gkanwar/unchat-keeb/images/unchat_2023/3d.png

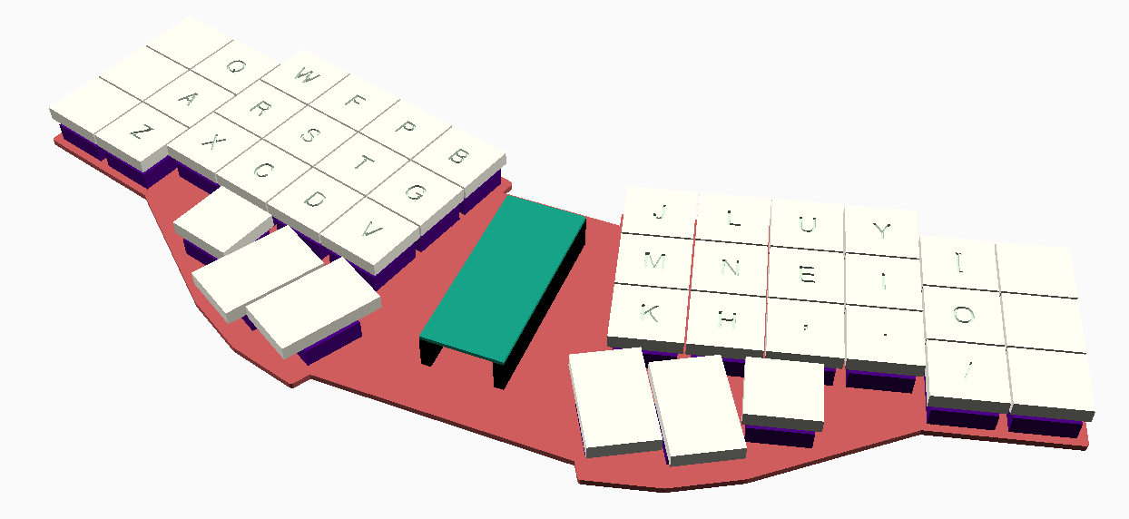
images/unchat_2023/3d.png
