gkanwar/unchat-keeb/images/unchat_2023/photo_top_no_keycaps.jpg

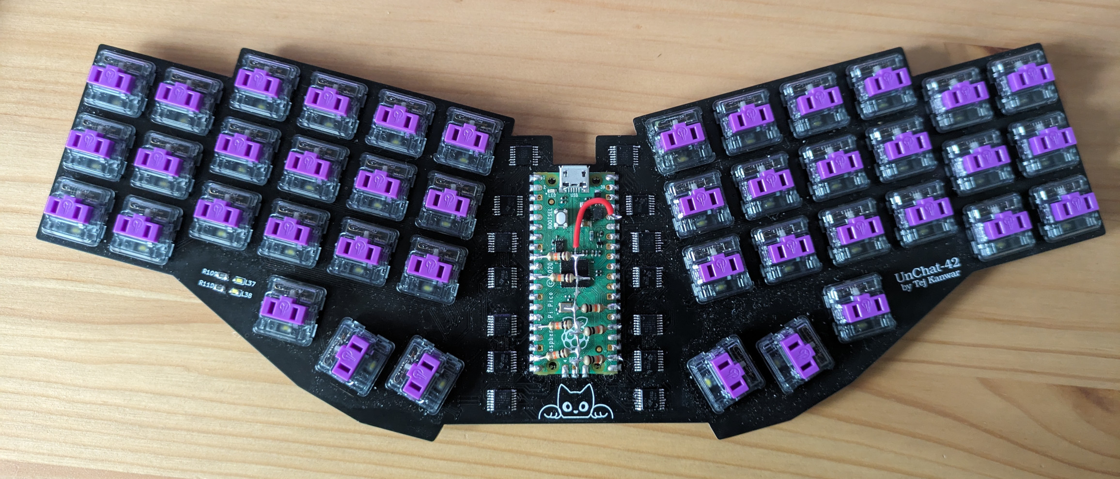
images/unchat_2023/photo_top_no_keycaps.jpg
