gkanwar/unchat-keeb/images/unchat_2024/photo_both_no_keycaps.jpg

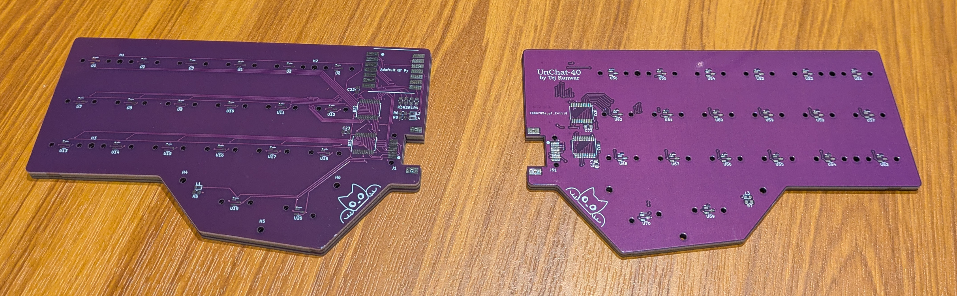
images/unchat_2024/photo_both_no_keycaps.jpg
