gkanwar/unchat-keeb/images/unchat_2024/photo_rhs_no_keycaps.jpg

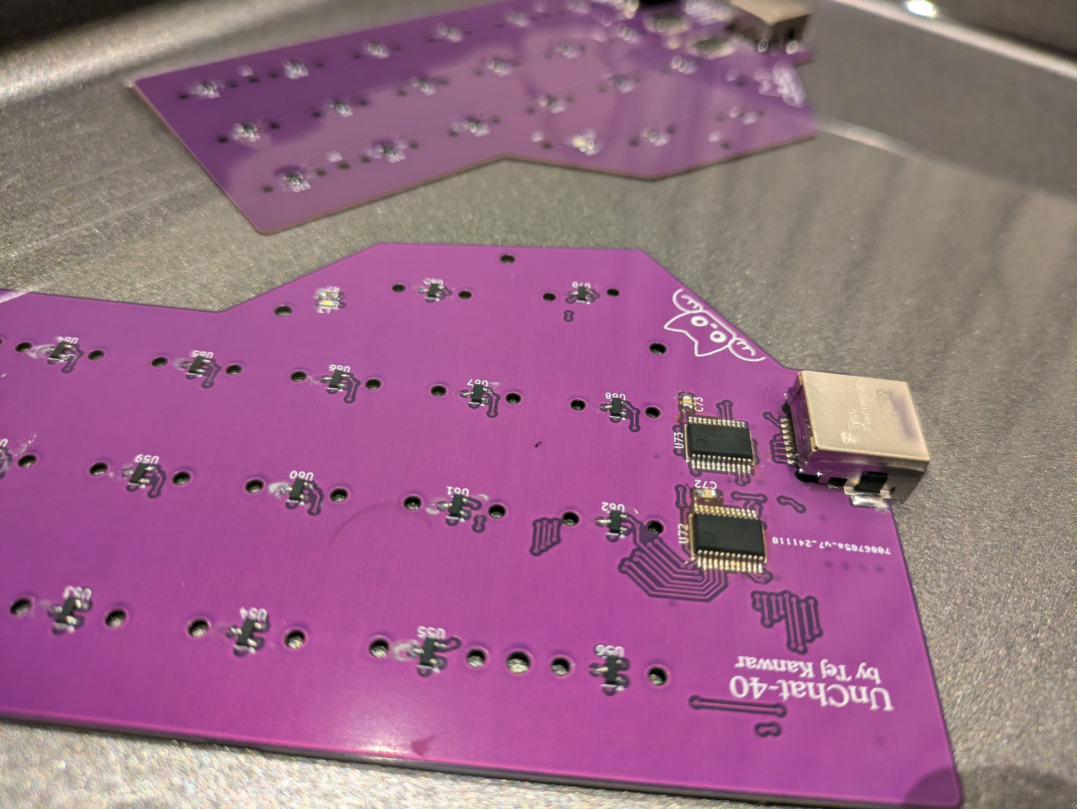
images/unchat_2024/photo_rhs_no_keycaps.jpg
