gkanwar/unchat-keeb/cad/pcb.scad

use <layout.scad>;

projection() pcb();

// projection(cut=true) layout(with_kc=false, with_pico=false);
