gkanwar/unchat-keeb/images/unchat_2023/photo_pcb_assembly.jpg

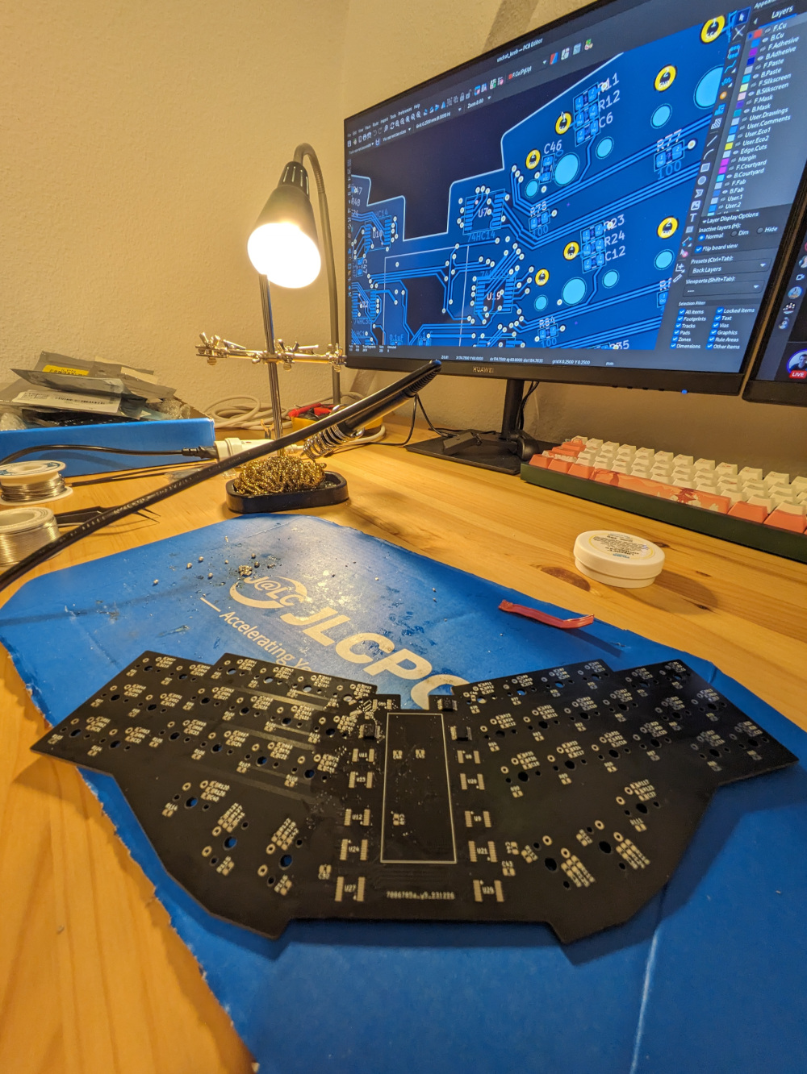
images/unchat_2023/photo_pcb_assembly.jpg
